janelia-idf/arduino_relay_mfc_controller/images/arduino_relay_mfc_controller_06_s.jpg

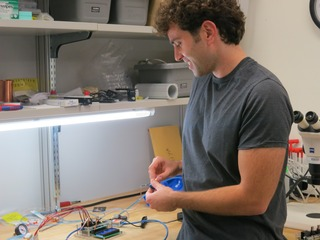
images/arduino_relay_mfc_controller_06_s.jpg
