janelia-idf/arduino_relay_mfc_controller/pcb/arduino_relay_mfc_controller.sch

## KiCad design pcb/arduino_relay_mfc_controller.sch (2019-02-07)

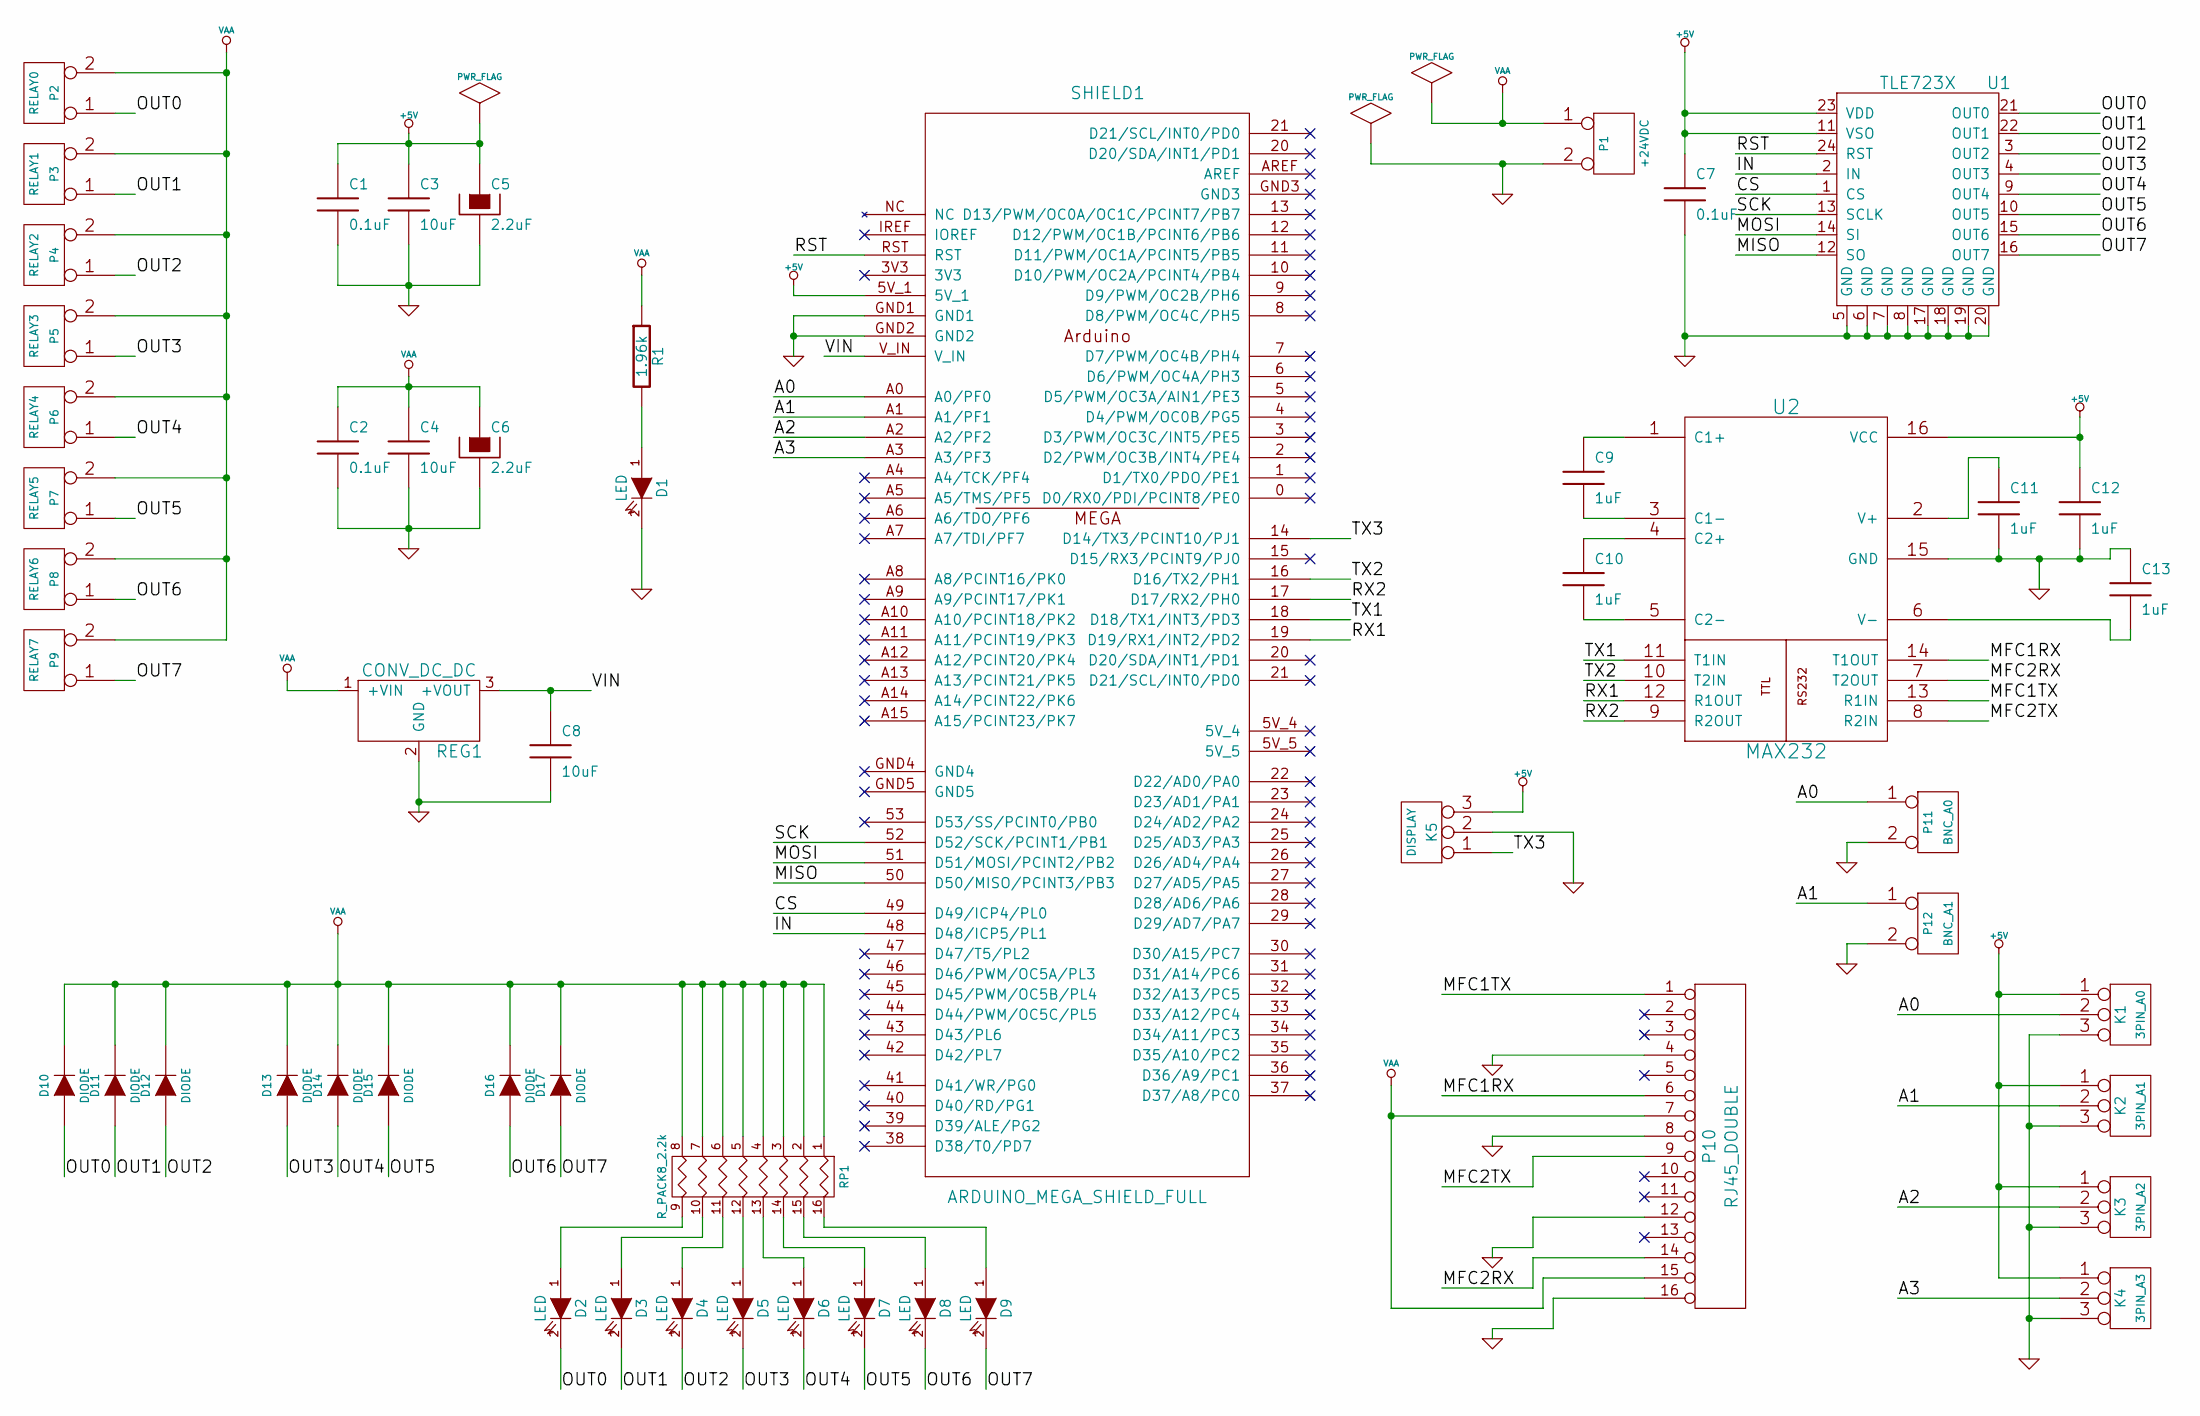
[picture p20: schematic arduino_relay_mfc_controller.sch]

Parts:
C1, C2, C7: 0.1uF
C3, C4, C8: 10uF
C5, C6: 2.2uF
C9, C10, C11, C12, C13: 1uF
D1, D2, D3, D4, D5, D6, D7, D8, D9: LED
D10, D11, D12, D13, D14, D15, D16, D17: DIODE
K1: 3PIN_A0
K2: 3PIN_A1
K3: 3PIN_A2
K4: 3PIN_A3
K5: DISPLAY
P1: +24VDC
P2: RELAY0
P3: RELAY1
P4: RELAY2
P5: RELAY3
P6: RELAY4
P7: RELAY5
P8: RELAY6
P9: RELAY7
P10: RJ45_DOUBLE
P11: BNC_A0
P12: BNC_A1
R1: 1.96k
REG1: CONV_DC_DC
RP1: R_PACK8_2.2k
SHIELD1: ARDUINO_MEGA_SHIELD_FULL
U1: TLE723X
U2: MAX232

Connections:
+5V: C1.1, C3.1, C5.1, C7.1, C12.1, K1.1, K2.1, K3.1, K4.1, K5.3, SHIELD1.5V_1, U1.11 (VSO), U1.23 (VDD), U2.16 (VCC)
A0: K1.2 (PM), P11.1, SHIELD1.A0 (A0/PF0)
A1: K2.2 (PM), P12.1, SHIELD1.A1 (A1/PF1)
A2: K3.2 (PM), SHIELD1.A2 (A2/PF2)
A3: K4.2 (PM), SHIELD1.A3 (A3/PF3)
CS: SHIELD1.49 (D49/ICP4/PL0), U1.1 (CS)
GND: C1.2, C2.2, C3.2, C4.2, C5.2, C6.2, C7.2, C8.2, C11.2, C12.2, C13.1, D1.2 (K), K1.3, K2.3, K3.3, K4.3, K5.2 (PM), P1.2 (PM), P10.4, P10.8, P10.12, P10.16, P11.2 (PM), P12.2 (PM), REG1.2 (GND), SHIELD1.GND1, SHIELD1.GND2, U1.5 (GND), U1.6 (GND), U1.7 (GND), U1.8 (GND), U1.17 (GND), U1.18 (GND), U1.19 (GND), U1.20 (GND), U2.15 (GND)
IN: SHIELD1.48 (D48/ICP5/PL1), U1.2 (IN)
MFC1RX: P10.6, U2.14 (T1OUT)
MFC1TX: P10.1, U2.13 (R1IN)
MFC2RX: P10.14, U2.7 (T2OUT)
MFC2TX: P10.9, U2.8 (R2IN)
MISO: SHIELD1.50 (D50/MISO/PCINT3/PB3), U1.12 (SO)
MOSI: SHIELD1.51 (D51/MOSI/PCINT2/PB2), U1.14 (SI)
unnamed: C9.1, U2.1 (C1+)
unnamed: C9.2, U2.3 (C1-)
unnamed: C10.1, U2.4 (C2+)
unnamed: C10.2, U2.5 (C2-)
unnamed: C11.1, U2.2 (V+)
unnamed: C13.2, U2.6 (V-)
unnamed: D1.1 (A), R1.2
unnamed: D2.1 (A), RP1.9 (R8)
unnamed: D3.1 (A), RP1.10 (R7)
unnamed: D4.1 (A), RP1.11 (R6)
unnamed: D5.1 (A), RP1.12 (R5)
unnamed: D6.1 (A), RP1.13 (R4)
unnamed: D7.1 (A), RP1.14 (R3)
unnamed: D8.1 (A), RP1.15 (R2)
unnamed: D9.1 (A), RP1.16 (R1)
OUT0: D2.2 (K), D10.1 (A), P2.1, U1.21 (OUT0)
OUT1: D3.2 (K), D11.1 (A), P3.1, U1.22 (OUT1)
OUT2: D4.2 (K), D12.1 (A), P4.1, U1.3 (OUT2)
OUT3: D5.2 (K), D13.1 (A), P5.1, U1.4 (OUT3)
OUT4: D6.2 (K), D14.1 (A), P6.1, U1.9 (OUT4)
OUT5: D7.2 (K), D15.1 (A), P7.1, U1.10 (OUT5)
OUT6: D8.2 (K), D16.1 (A), P8.1, U1.15 (OUT6)
OUT7: D9.2 (K), D17.1 (A), P9.1, U1.16 (OUT7)
RST: SHIELD1.RST, U1.24 (RST)
RX1: SHIELD1.19 (D19/RX1/INT2/PD2), U2.12 (R1OUT)
RX2: SHIELD1.17 (D17/RX2/PH0), U2.9 (R2OUT)
SCK: SHIELD1.52 (D52/SCK/PCINT1/PB1), U1.13 (SCLK)
TX1: SHIELD1.18 (D18/TX1/INT3/PD3), U2.11 (T1IN)
TX2: SHIELD1.16 (D16/TX2/PH1), U2.10 (T2IN)
TX3: K5.1, SHIELD1.14 (D14/TX3/PCINT10/PJ1)
VAA: C2.1, C4.1, C6.1, D10.2 (K), D11.2 (K), D12.2 (K), D13.2 (K), D14.2 (K), D15.2 (K), D16.2 (K), D17.2 (K), P1.1, P2.2 (PM), P3.2 (PM), P4.2 (PM), P5.2 (PM), P6.2 (PM), P7.2 (PM), P8.2 (PM), P9.2 (PM), P10.7, P10.15, R1.1, REG1.1 (+VIN), RP1.1, RP1.2, RP1.3, RP1.4, RP1.5, RP1.6, RP1.7, RP1.8
VIN: C8.1, REG1.3 (+VOUT), SHIELD1.V_IN
